g1sbi/qaz-cyberdeck/images/case.jpg

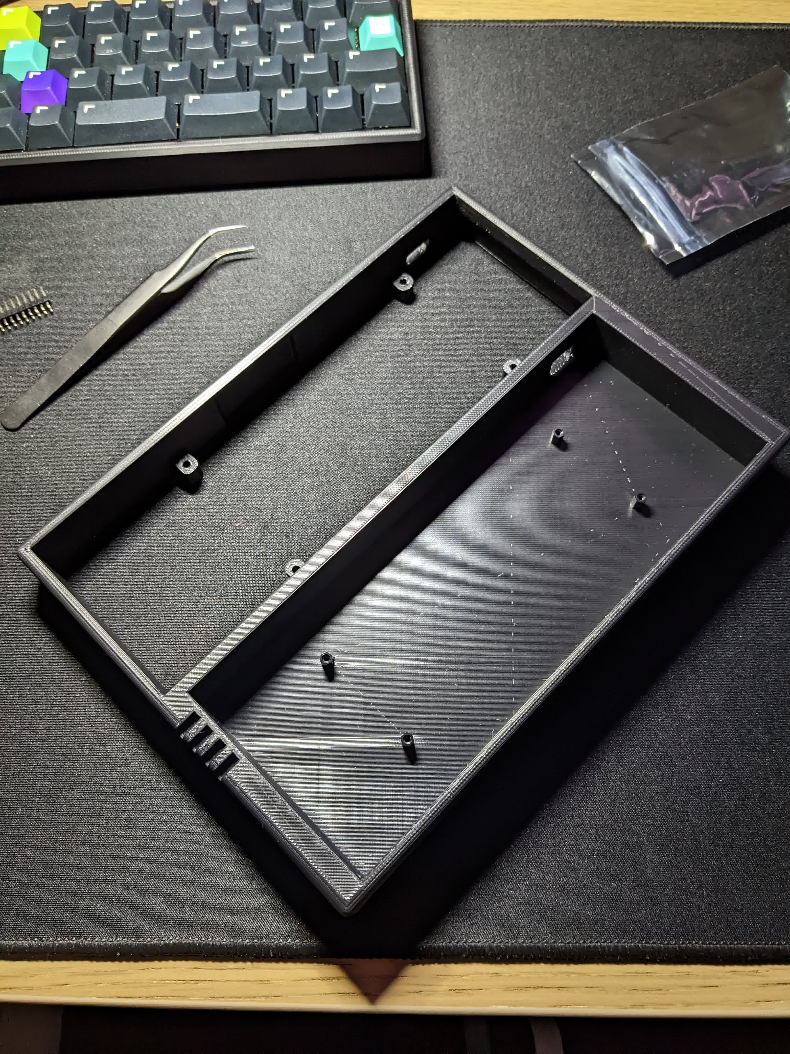
images/case.jpg
